postfalk/z80/z80asm/d88.asm

;;;;;;;;;;;;;;;;;;;;;;;;;;;;;;;;;;;;;;;;;;;;;;;;;;;;;;;;;;;;;;;;;;;;;;;;;;
;                                                                        ;
;  This is a software implementation of I2C for my little Z80 project    ;
;  ==================================================================    ;
;  It currently drives Adafruits LED backpacks based on ht16k33 chip     ;
;                                                                        ;
;  See datasheet here                                                    ;
;  http://www.adafruit.com/datasheets/ht16K33v110.pdf                    ;
;                                                                        ;
;;;;;;;;;;;;;;;;;;;;;;;;;;;;;;;;;;;;;;;;;;;;;;;;;;;;;;;;;;;;;;;;;;;;;;;;;;

; TODO; streamline!

org 00000h

setup:              ld sp, 0ffffh       ; set stack pointer
                    ld hl, 00ff00h      ; begin page to store datasheet
                    ld a, 00fh          ; set PIO B to output mode
                    out (03h),a         ;
                    ld a, 00h           ; set PIO B OUT to 00fh
                    out (02h),a         ;
                    ld a, 03h
                    call output
                    ld bc, 01h          ; waiting for power-on-reset
                    call wait           ; of display finished
                    call backpack_on

loop:               ld hl, display
                    call write_frame
    loop2:          ld a, 01h
                    call output
                    ld a, 03h
                    call output
                    jp loop2            ; just hanging out here for now

backpack_on:        call startTransmission
                    ; start oscillator
                    ld a, 021h
                    call write
                    call endTransmission
                    ; set brightness
                    call startTransmission
                    ld a, 0e0h
                    call write
                    call endTransmission
                    ; turn display on
                    call startTransmission
                    ld a, 081h
                    call write
                    call endTransmission
                    ret

write_frame:        call startTransmission
                    ld a, 00h
                    call write
                    ld b, 08h
    lp10:           ld a, (hl)
                    call write
                    ld a, 00h
                    call write
                    inc hl
                    dec b
                    jp nz, lp10
                    call endTransmission
                    ret

; use terminology similar to Wire.h C-library
startTransmission:  ld a, 03h
                    call output
                    ld bc, 01h      ; this wait is really required
                    call wait       ; but could probably be shorter
                    ld a,02h
                    call output
                    ld a, 0e0h      ; call device address, move to variable as needed
                    call write
                    ret

endTransmission:    ld a, 00h
                    call output
                    ld a, 02h
                    call output
                    ld a, 03h
                    call output
                    ld bc, 01h      ; this wait is required 
                    call wait       ; but could be shorter
                    ret

write:              push bc
                    ld b, 008h      ; for i=0 to 7
                    ld c, a         ; using c here since I have to push bc anyways
    lp1:            rlc c           ; rotate to left so that most significant bit becomes least significant
                    ld a, 001h      ; load mask
                    and c           ; and deletes all not masked bits
                    call clbit
                    dec b
                    jp nz, lp1
                    call ackn
                    pop bc
                    ret

; clock cycle around bit, from register a
; removed getting back to original state
; seems to work without it
clbit:              push bc
                    call output
                    or 002h
                    call output
                    and 001h
                    call output
                    pop bc
                    ret

; send acknowledge sequence
; TODO: actually acknowledge and not
; just assume ok
ackn:               
                    ld a, 001h
                    call output
                    ld a, 003h
                    call output
                    ret

; simulate open drain by switching 
; between PIOs output modes
; see http://members.iinet.net.au/~daveb/downloads/Z80.zip
output:             ld c, 003h
                    ld b, 0cfh ; was 0cfh do not remember why
                    out(c), b
                    out(c), a
                    ret

; set relative wait time in bc
wait:               push de         ; protect affected registers
                    push af
    outer:          ld de, 0100h
        inner:      dec de
                    ld a, d
                    or e
                    jp nz, inner
                    dec bc
                    ld a, b
                    or c
                    jp nz, outer
                    pop af
                    pop de
                    ret

; store data here
display:            db 01eh, 021h, 0d2h, 0c0h, 0d2h, 0cch, 021h, 01eh
